evemorgen/PuszkoSatelita/dokumentacja/prezentacje_esero/07_Zaawansowane.pdf

# Zaawansowane konstrukcje CanSat

WARSZTATY CANSAT


# Zaawansowane CanSaty

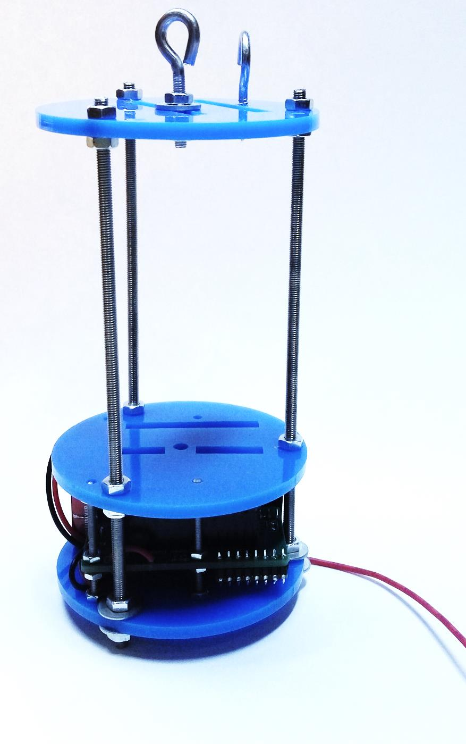
[picture p26: figure]

Podstawowa misja CanSat…

…zajmuje mniej niż połowę dostępnego miejsca! Warto je wykorzystać…

Na co wykorzystać dostępne miejsce

i zasoby ?

- zapewnienie większej niezawodności misji podstawowej
- misja zaawansowana

# Redundancja danych

- Łącze radiowe jest zawodne
- Warto zabezpieczyć się zapisując dane w samym CanSatcie, tak aby odzyskać je po lądowaniu

Jakie są możliwości?

- zapisanie newralgicznych danych w pamięci EEPROM uC Atmega: 1K wystarczy na zapisanie 512 pomiarów z ADC (czyli np. ciśnienia i temperatury)
- zewnętrzne pamięci flash (kilka MB) podłączone do komputera pokładowego
- karta SD (Gigabajty)

# Redundancja danych – karta SD

karta SD
(podłączona do SPI)

karta SD
(moduł na UART)

np.
AK-SDFS-UART

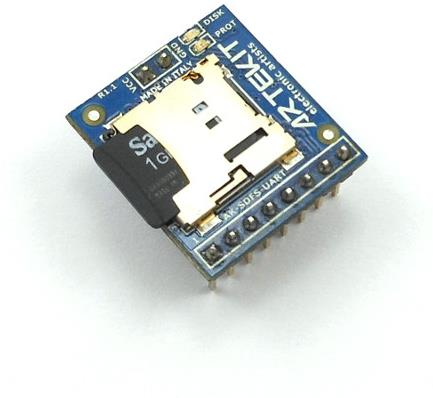
[picture p27: figure]
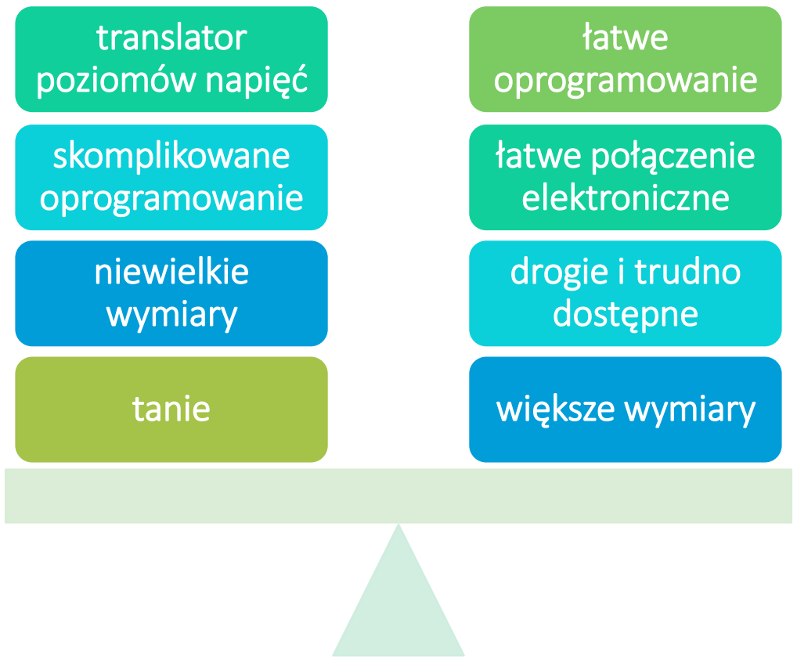
[picture p28: figure]
większe wymiary; drogie i trudno dostępne; łatwe połączenie elektroniczne; łatwe oprogramowanie; tanie; niewielkie wymiary; skomplikowane oprogramowanie; translator poziomów napięć

# Redundancja danych – karta SD

- biblioteka do użycia kart SD z Arduino
- przykład Datalogger

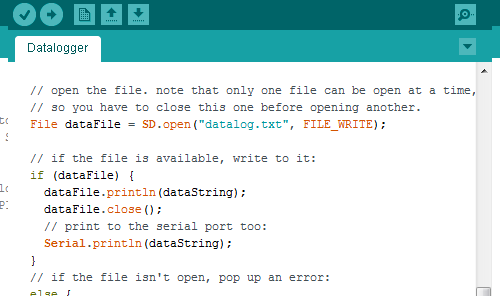
[picture p29: figure]

# Misje dodatkowe

- Sonda planetarna
- Precyzyjne lądowanie
- System odzyskiwania
- Zaawansowana telemetria
- Zaawansowana łączność radiowa

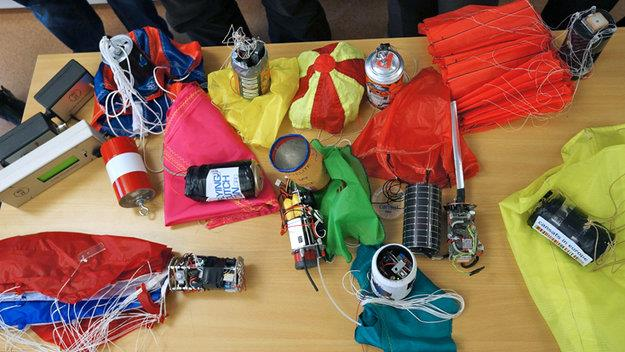
[picture p30: figure]

# Sonda planetarna

Rejestracja danych z czujników podczas spadania przez atmosferę i na powierzchni po lądowaniu.

Co może badać CanSat? Np.:

- wilgotność
- skład atmosfery
- natężenie światła widzialnego
- natężenie promieniowania UV, IR,
- spektrometria
- dokładniejsze pomiary temperatury

# Sonda planetarna

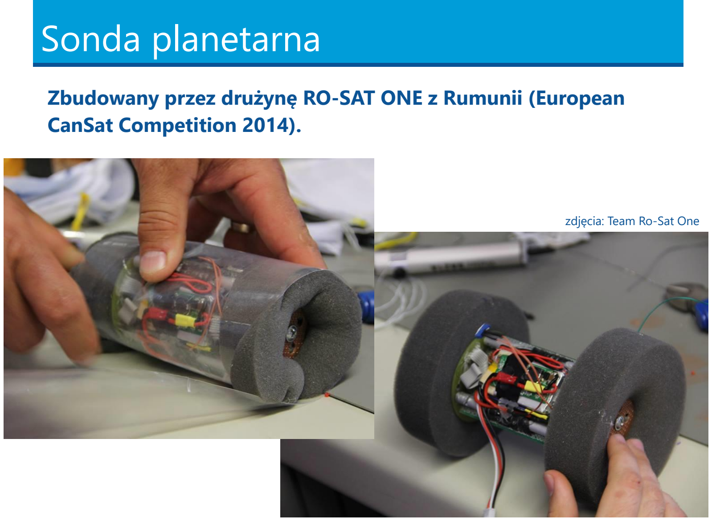
[picture p31: page 8]

Zbudowany przez drużynę RO-SAT ONE z Rumunii (European CanSat Competition 2014).

zdjęcia: Team Ro-Sat One

# Precyzyjne lądowanie

Misją CanSatu jest wylądowanie we wcześniej określonym miejscu.

- naprowadzanie ręczne / autonomiczne
- wykorzystanie glajtu i serwomechanizmów do sterowania
- wykorzystanie geolokalizacji GPS

# System odzyskiwania

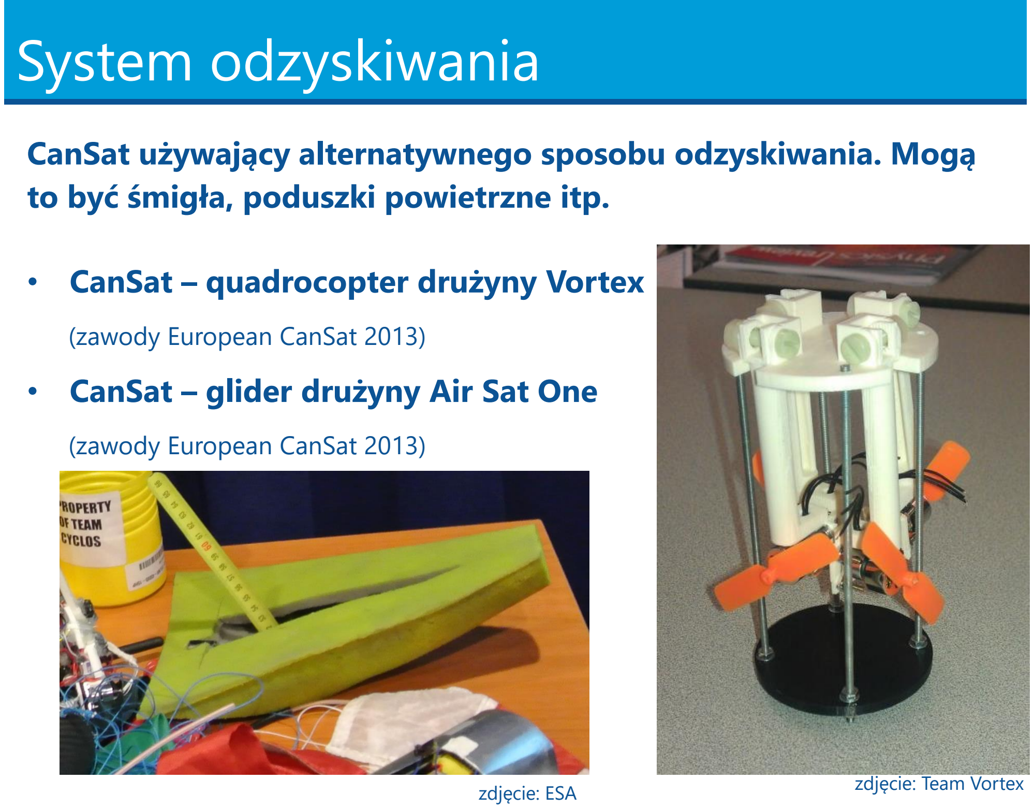
[picture p32: page 10]

CanSat używający alternatywnego sposobu odzyskiwania. Mogą to być śmigła, poduszki powietrzne itp.

- CanSat – quadrocopter drużyny Vortex

(zawody European CanSat 2013)
- CanSat – glider drużyny Air Sat One

(zawody European CanSat 2013)

zdjęcie: Team Vortex zdjęcie: ESA

# Zaawansowana telemetria

Rejestracja danych z dużą częstotliwością z czujników podczas lotu rakietą, jak i opadania.

CanSat może wykorzystać:

- Inertial Measurement Unit 11DOF:
- akcelerometr, żyroskop, magnetometr, barometr, termometr
- GPS

Zaawansowana obróbka danych:

np. Określanie toru ruchu w przestrzeni na podstawie czujników IMU i porównanie ze wskazaniami GPS.

# Zaawansowana łączność radiowa

Celem misji jest wykorzystywanie i przetestowanie zaawansowanej łączności radiowej, szczególnie:

- łączność w dwie strony
- przesyłanie dużych ilości danych z czujników
- przesyłanie zdjęć, obrazu z kamery

Q&A
