evemorgen/PuszkoSatelita/dokumentacja/prezentacje_esero/05_Projektowanie.pdf

# Projektowanie elektroniki

WARSZTATY CANSAT

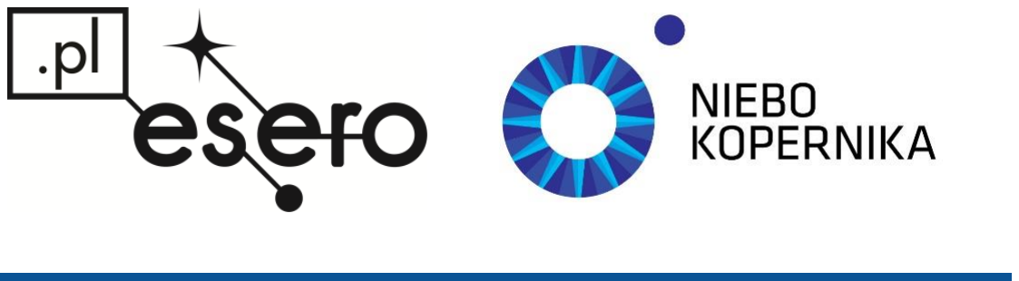
[picture p66: figure]

# Od pomysłu, do układu

Projektowanie układów to

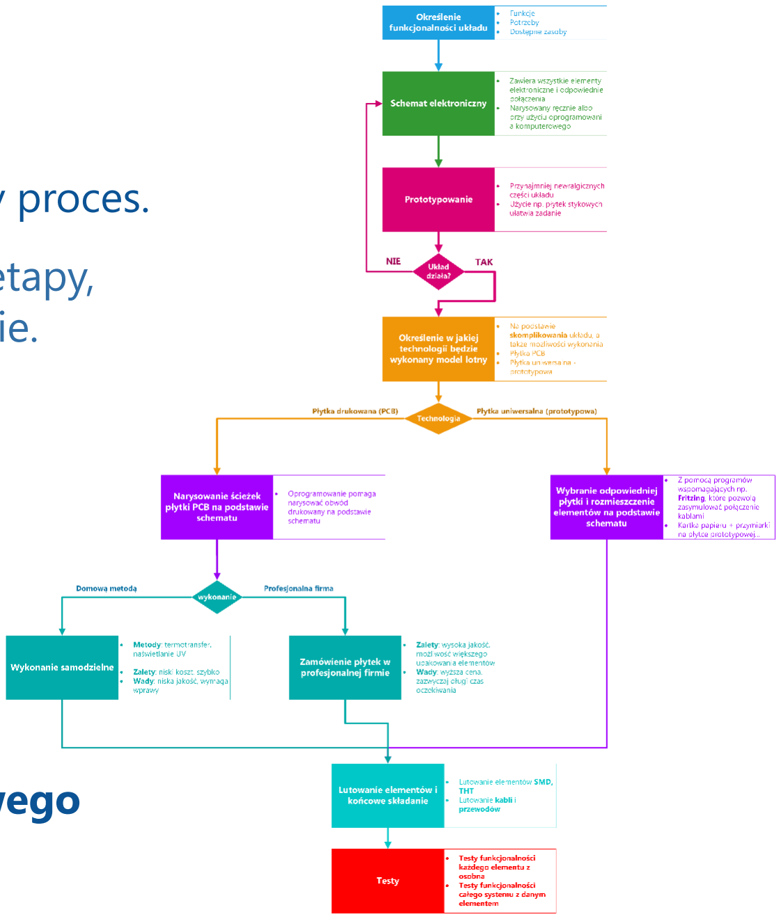
[picture p67: figure]

skomplikowany i czasochłonny proces.

Rozbicie go na poszczególne etapy, może znacznie uprościć zadanie.

- pomysł
- projekt
- testy prototypu
- ewentualne poprawki
- wykonanie modelu końcowego
- testy

# Określenie funkcjonalności układu

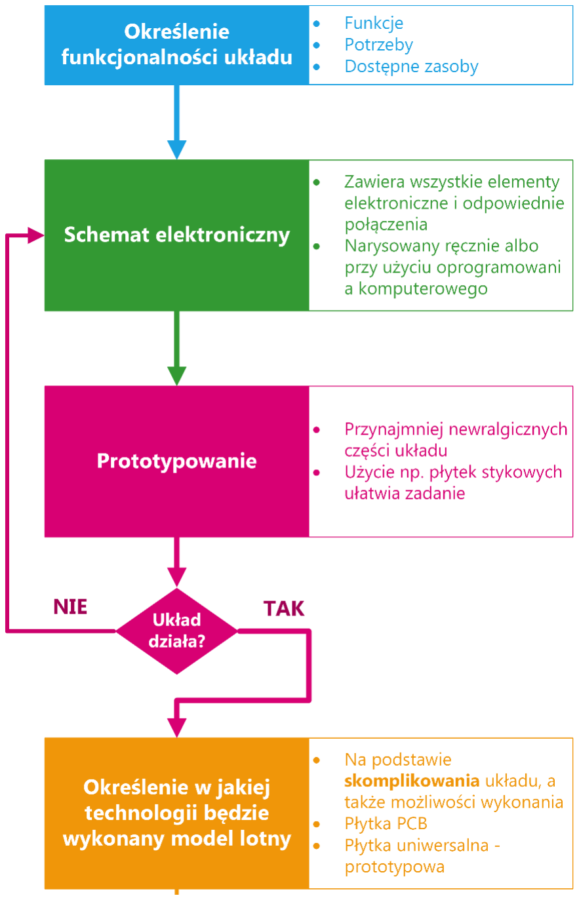
[picture p68: figure]

- Jakie funkcje ma spełniać układ?
- Z czym ma współpracować (być połączony)?
- Jakie mamy zasoby:
- technologiczne
- finansowe
- ludzkie

# Schemat elektroniczny

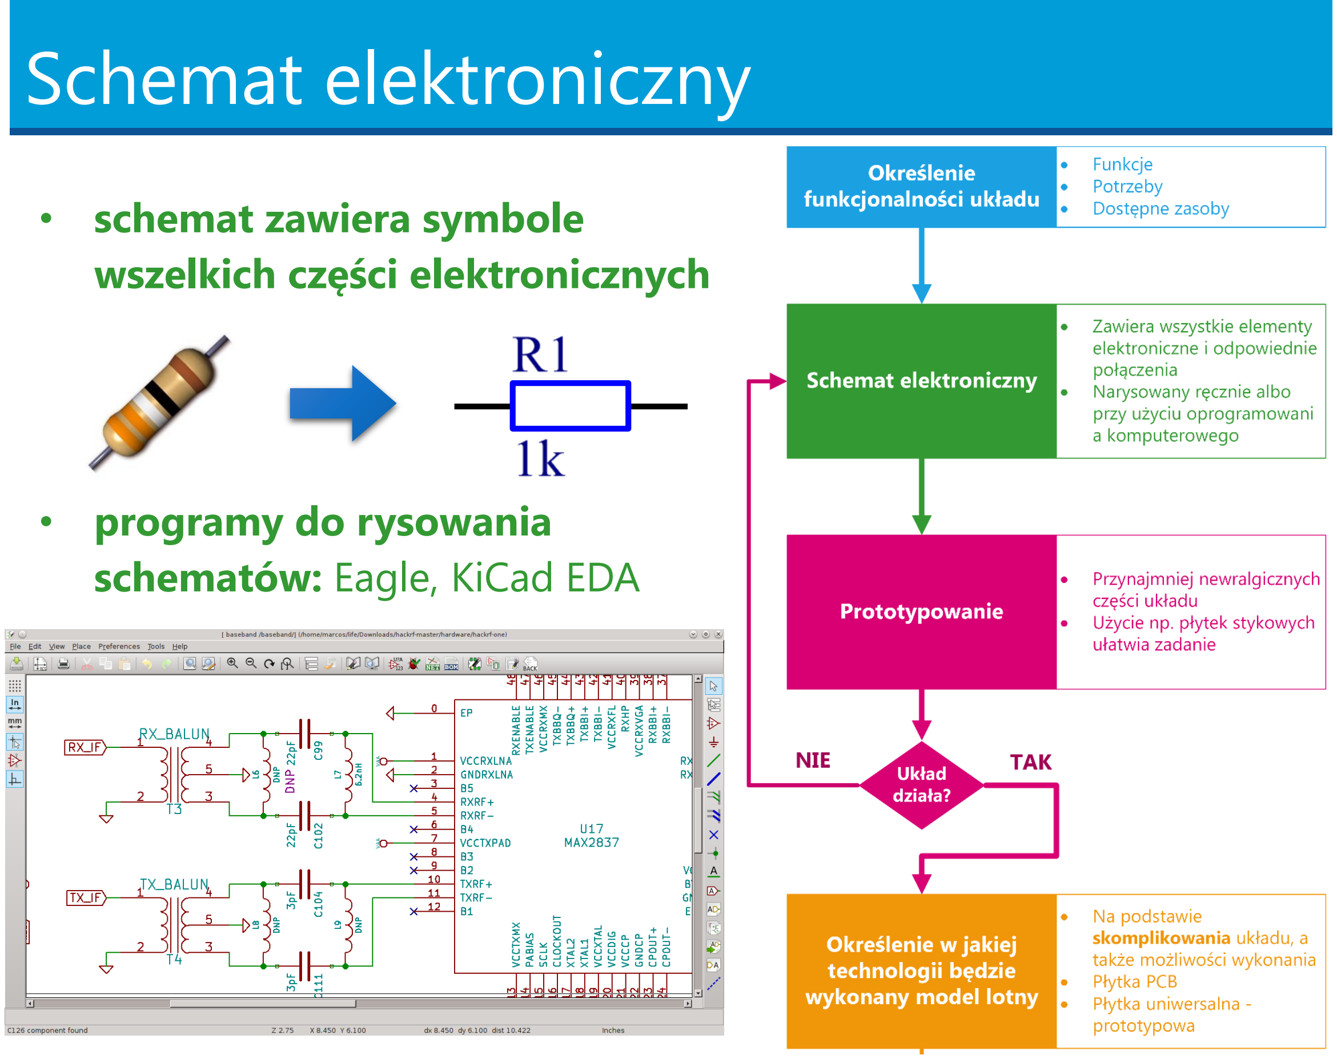
[picture p69: page 4]

- schemat zawiera symbole
wszelkich części elektronicznych
- programy do rysowania
schematów: Eagle, KiCad EDA

# Prototypowane

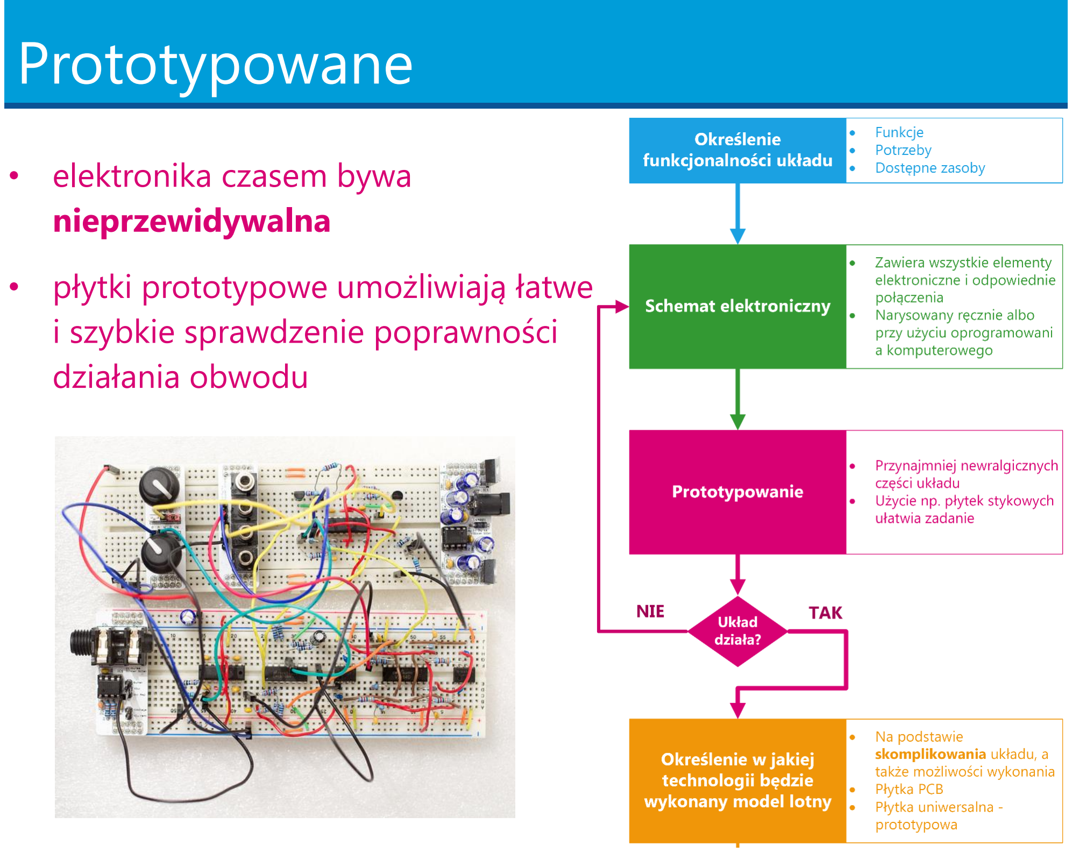
[picture p70: page 5]

- elektronika czasem bywa
nieprzewidywalna
- płytki prototypowe umożliwiają łatwe i szybkie sprawdzenie poprawności działania obwodu

# Prototypowane

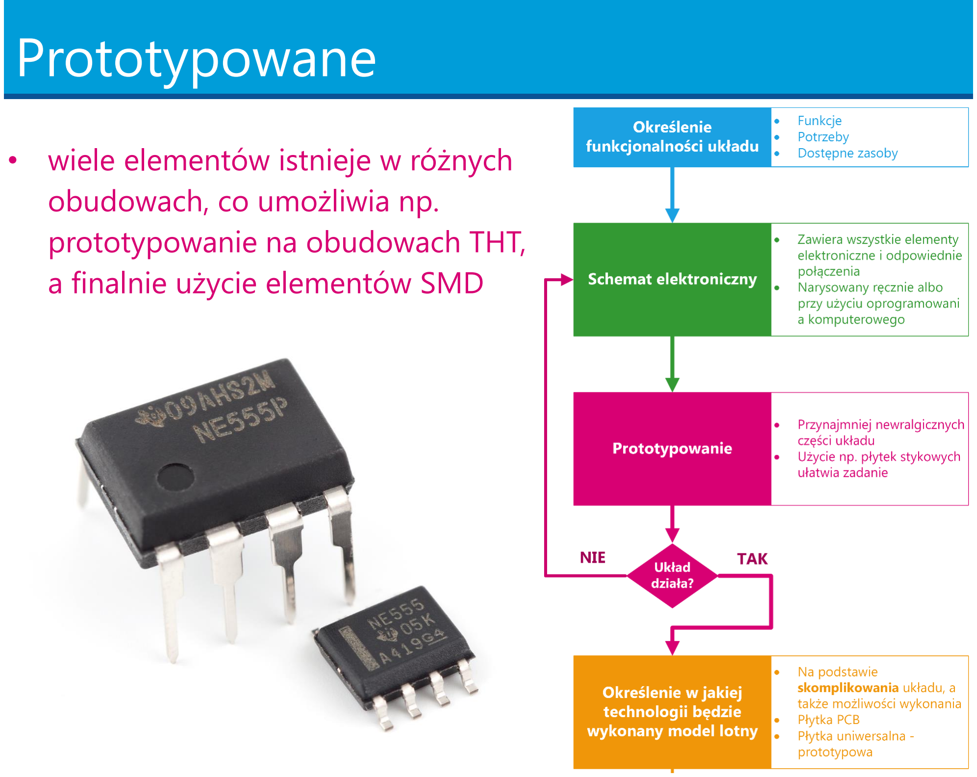
[picture p71: page 6]

- wiele elementów istnieje w różnych obudowach, co umożliwia np. prototypowanie na obudowach THT, a finalnie użycie elementów SMD

# Określenie technologii wykonania

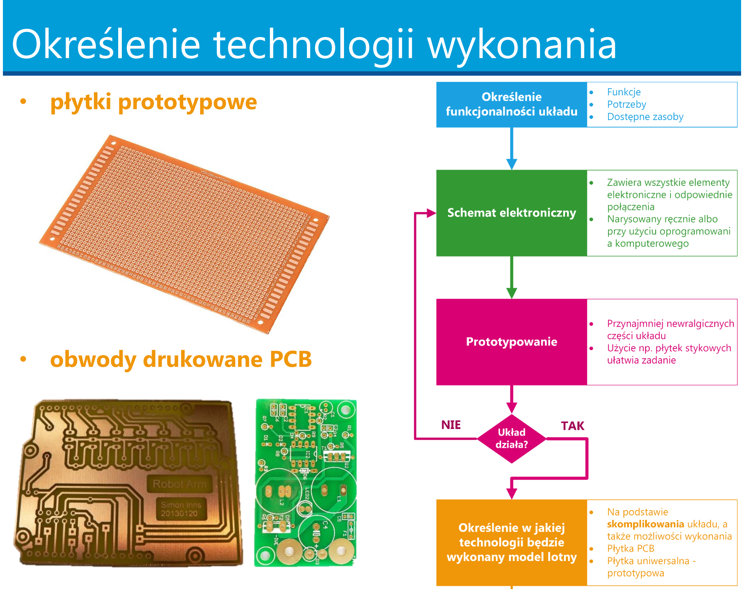
[picture p72: page 7]

- płytki prototypowe
- obwody drukowane PCB

# Płytka uniwersalna (prototypowa)

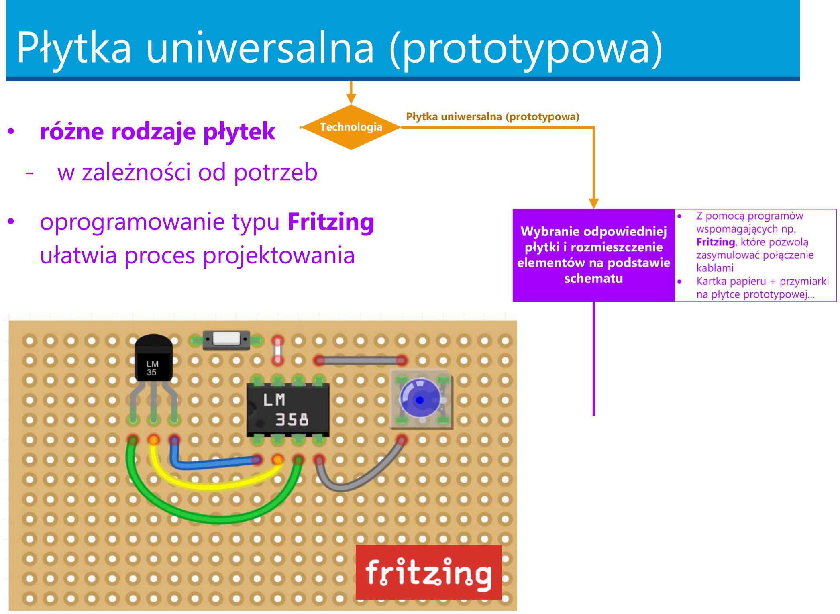
[picture p73: page 8]

- różne rodzaje płytek
- w zależności od potrzeb
- oprogramowanie typu Fritzing ułatwia proces projektowania

# Określenie technologii wykonania

- płytki prototypowe
- obwody drukowane PCB

# Tworzenie obwodu drukowanego

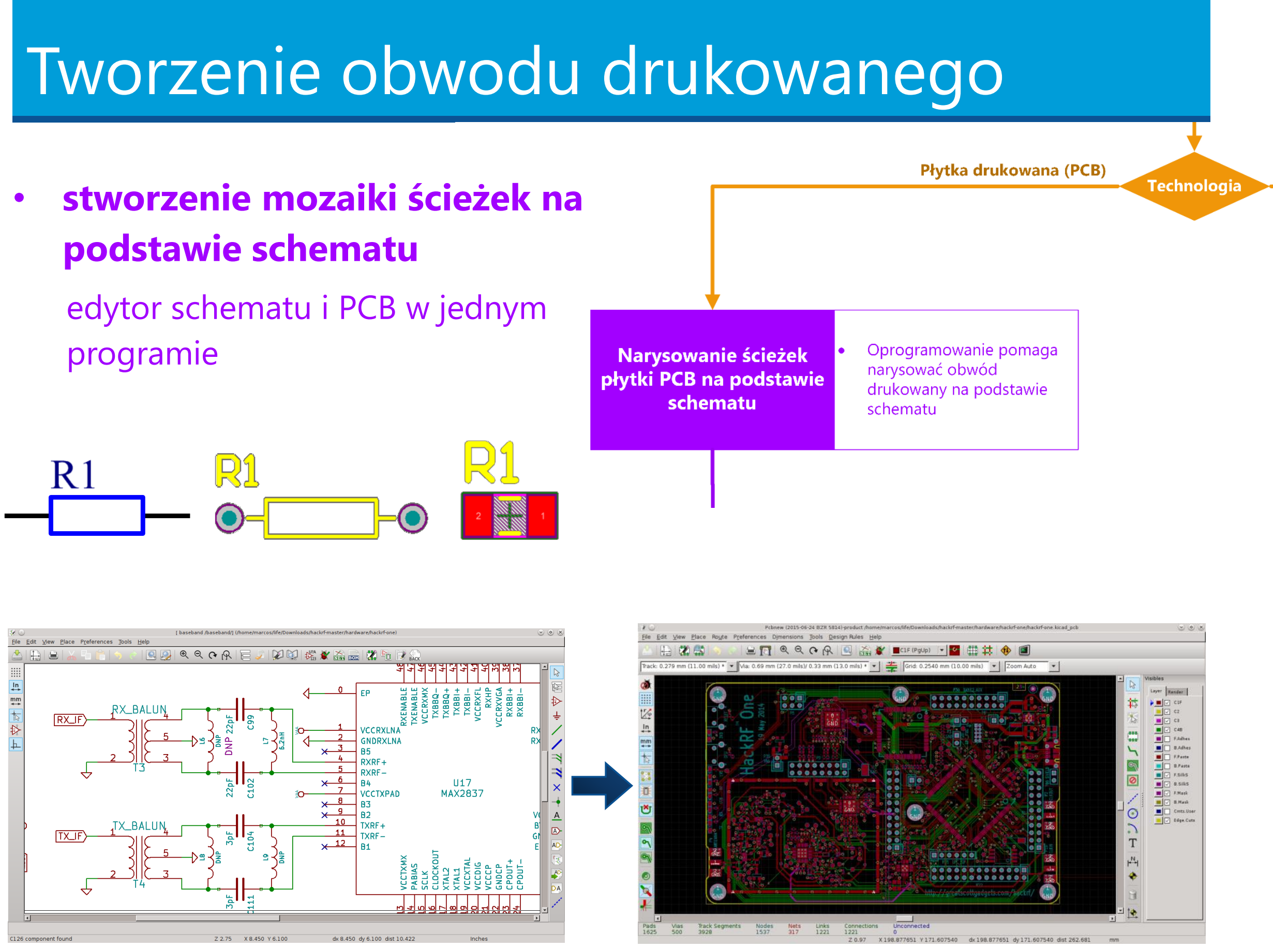
[picture p74: page 10]

- stworzenie mozaiki ścieżek na podstawie schematu

edytor schematu i PCB w jednym programie

# Tworzenie obwodu drukowanego

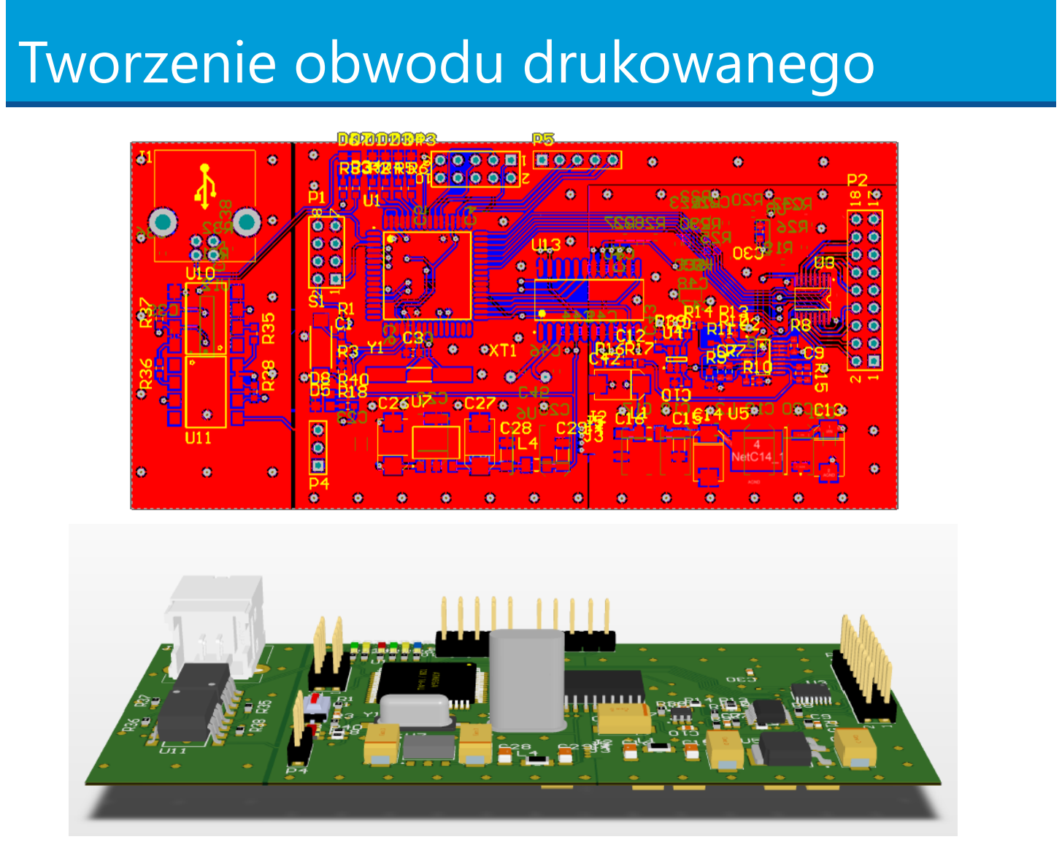
[picture p75: page 11]

# Tworzenie obwodu drukowanego

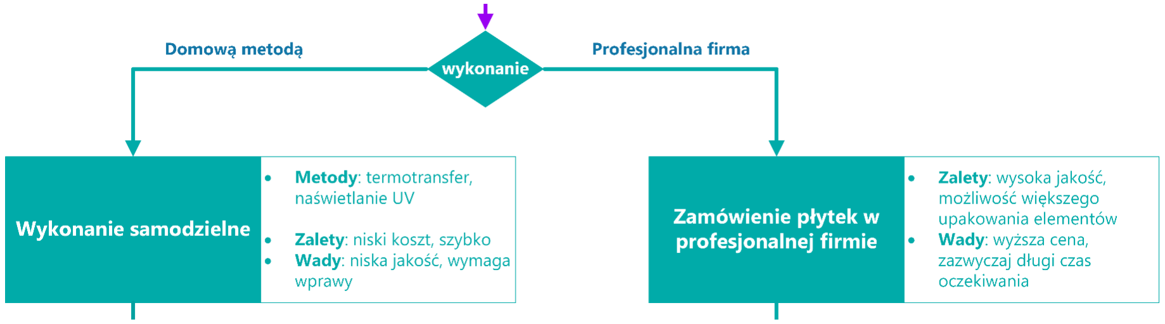
[picture p76: figure]

- wymaga pewnego
doświadczenia (kilku prób)
- dużo tutoriali dostępnych w Internecie
- niewielkie koszty
- niezbyt czasochłonne
- możliwość zrobienia dużo bardziej skomplikowanej płytki
- dużo lepsza jakość wykonania
- łatwiejsze lutowanie i
niezawodność
- długi czas oczekiwania
- wyższa cena

# Lutowanie

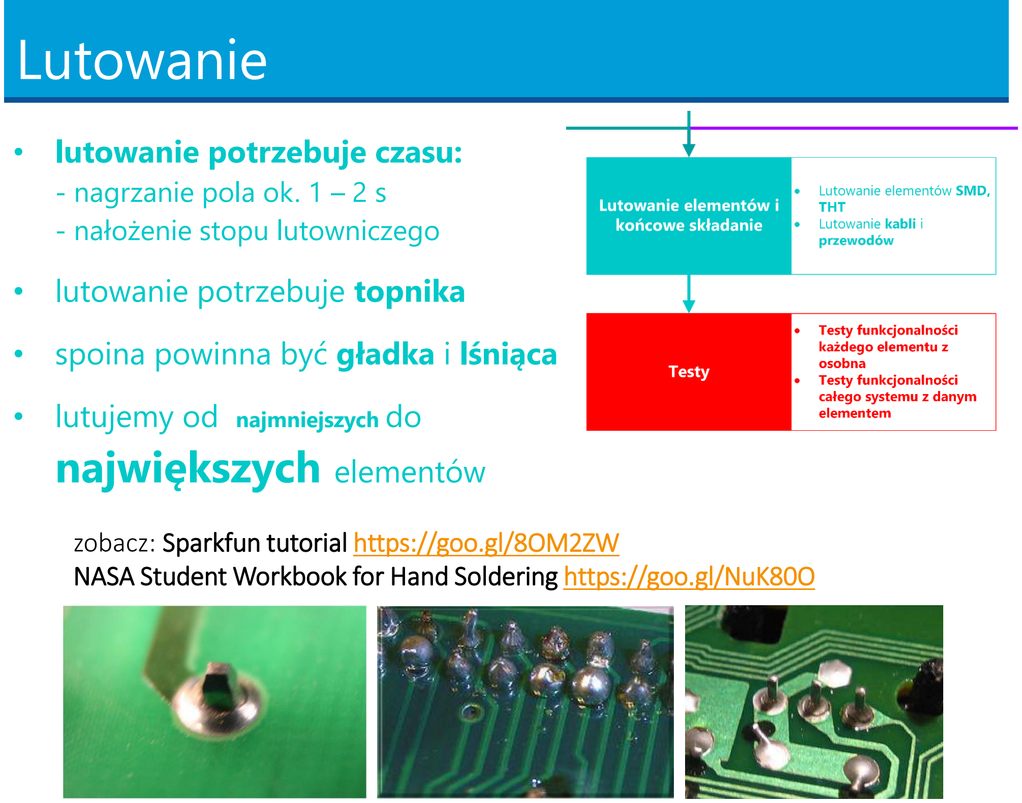
[picture p77: page 13]

- lutowanie potrzebuje czasu:
- nagrzanie pola ok. 1 – 2 s
- nałożenie stopu lutowniczego
- lutowanie potrzebuje topnika
- spoina powinna być gładka i lśniąca
- lutujemy od najmniejszych do

## największych elementów

zobacz: Sparkfun tutorial https://goo.gl/8OM2ZW
NASA Student Workbook for Hand Soldering https://goo.gl/NuK80O

# Lutowanie

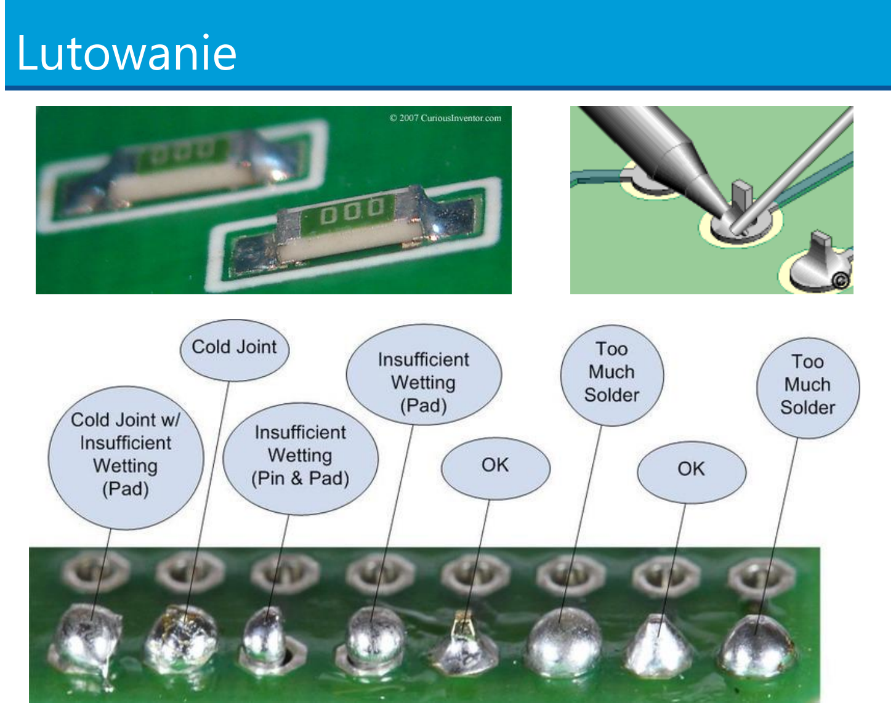
[picture p78: page 14]

# Testy

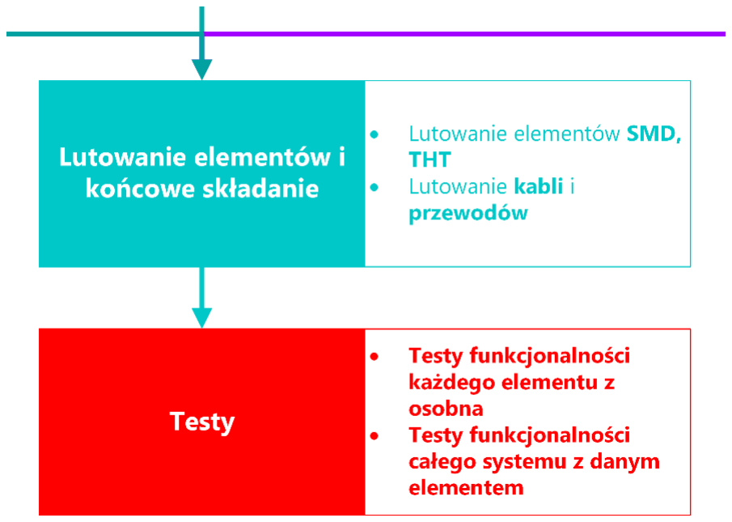
[picture p79: figure]

- testy są ważne
- tylko jedna szansa wysłania CanSata
- testy mechaniczne i optyczne
- brak zwarć i przerw, zimnych lutów
- testy elektroniczne
- działanie samego układu
- współpraca układu z resztą systemu
- testy symulujące warunki misji

# Podsumowanie

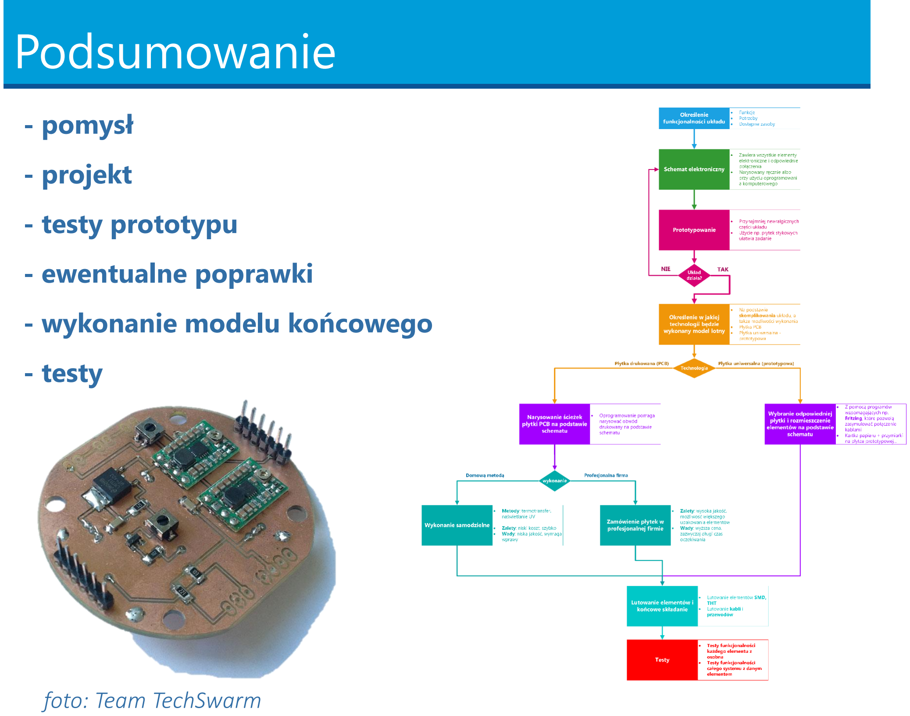
[picture p80: page 16]

- pomysł
- projekt
- testy prototypu
- ewentualne poprawki
- wykonanie modelu końcowego
- testy

foto: Team TechSwarm

Q&A
